ChasinSpin/SkyPilot/pifinder/3DPrinted/PiFinderLensCover/PiFinderLensCover.3mf

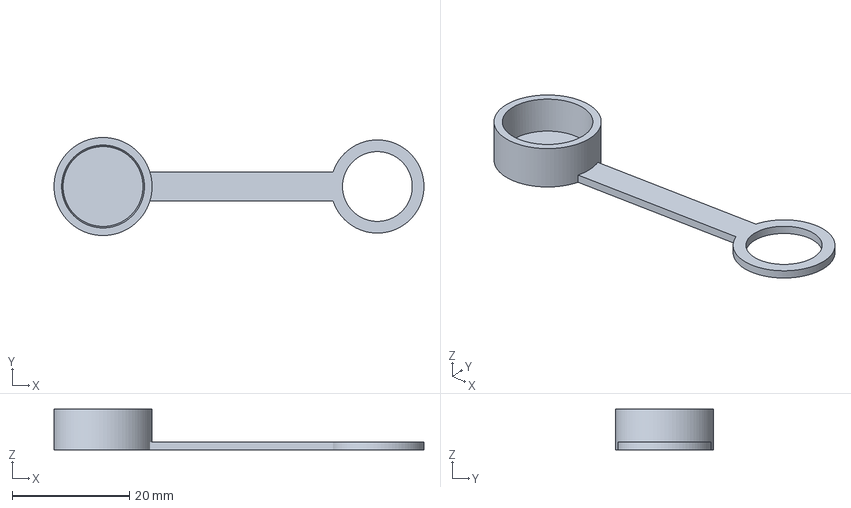
[picture p20: CAD file, 2024-11-16]
pifinder/3DPrinted/PiFinderLensCover/PiFinderLensCover.3mf
63.0 x 16.7 x 6.90 mm
