ChasinSpin/SkyPilot/dome/GPS/GPSCableClip.3mf

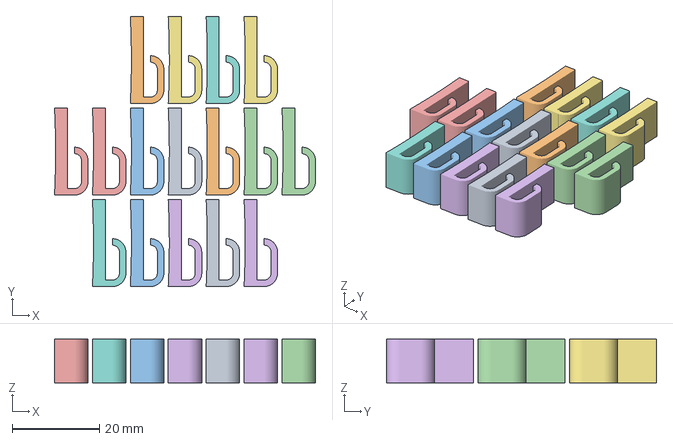
[picture p21: CAD file, 2024-11-11]
dome/GPS/GPSCableClip.3mf
59.9 x 62.0 x 10.0 mm
GPSCableClip.stl x 16
