ChasinSpin/SkyPilot/dome/TriBahtinovMask_ClubC14/TriBahtinovCover.3mf

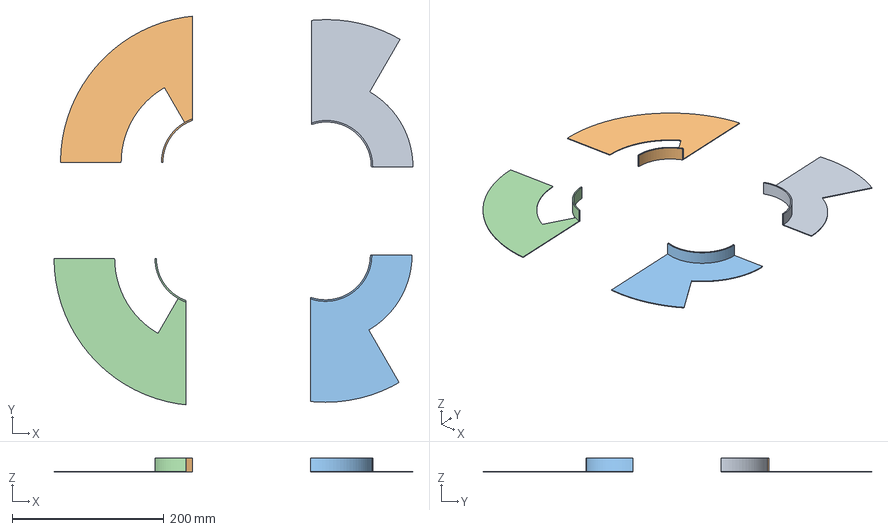
[picture p22: CAD file, 2025-02-14]
dome/TriBahtinovMask_ClubC14/TriBahtinovCover.3mf
473.1 x 512.0 x 19.0 mm
TriBahtinovCover.stl_A_A
TriBahtinovCover.stl_A_B
TriBahtinovCover.stl_B_A
TriBahtinovCover.stl_B_B
