ChasinSpin/SkyPilot/goto/3DPrinted/decRJ45Plate.3mf

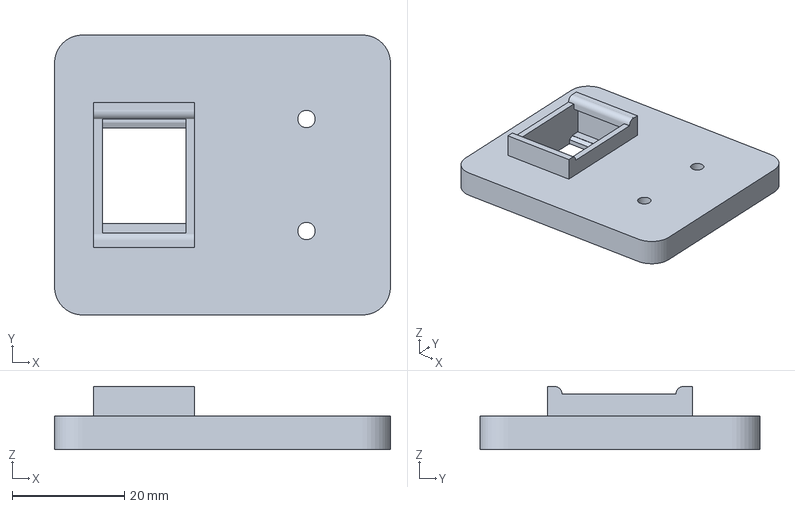
[picture p23: CAD file, 2025-01-19]
goto/3DPrinted/decRJ45Plate.3mf
60.0 x 50.0 x 11.2 mm
