ChasinSpin/SkyPilot/pifinder/3DPrinted/C14PiFinderHolder/clamp.stl

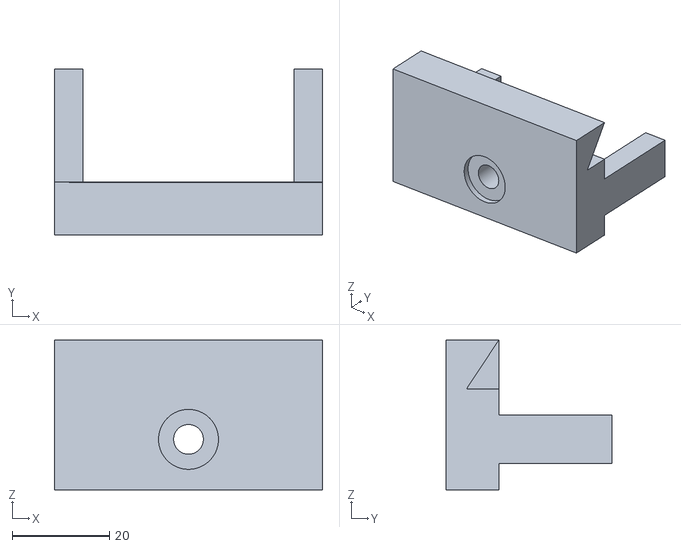
[picture p24: CAD file, 2024-11-16]
pifinder/3DPrinted/C14PiFinderHolder/clamp.stl
55.0 x 34.0 x 30.7
