ChasinSpin/SkyPilot/pifinder/3DPrinted/PiFinder/shroud.stl

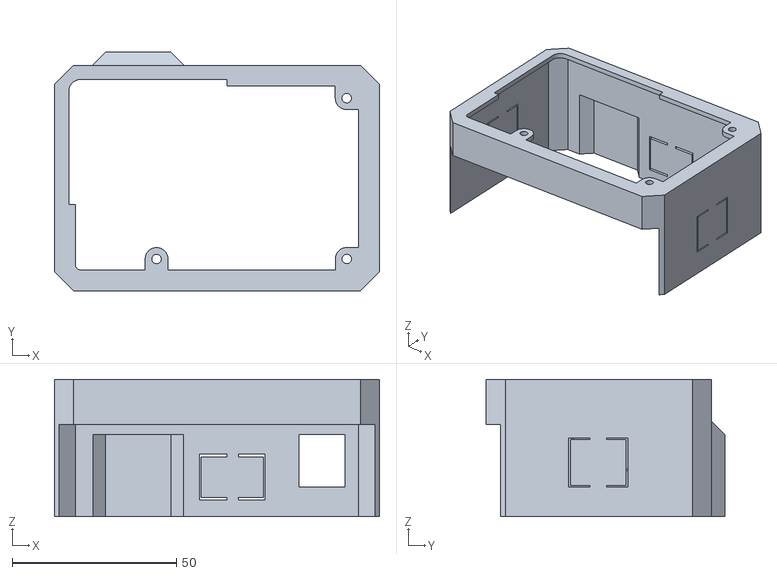
[picture p25: CAD file, 2024-11-16]
pifinder/3DPrinted/PiFinder/shroud.stl
99.1 x 72.7 x 41.8
