ChasinSpin/SkyPilot/dome/GPS/GPSBracketCovers.3mf

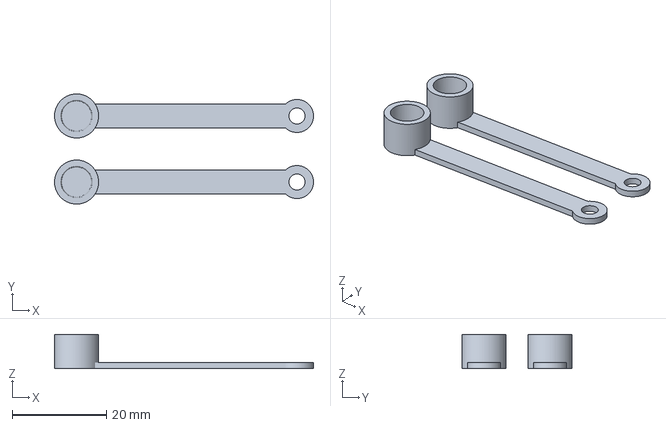
[picture p26: CAD file, 2024-11-11]
dome/GPS/GPSBracketCovers.3mf
54.9 x 23.3 x 7.30 mm
