ChasinSpin/SkyPilot/dome/TriBahtinovMask_ClubC14/TriBahtinovMask.3mf

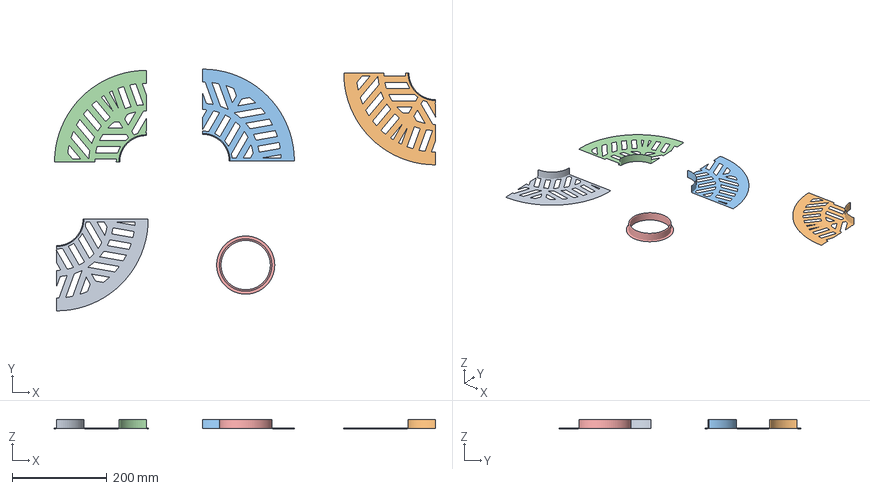
[picture p27: CAD file, 2025-02-14]
dome/TriBahtinovMask_ClubC14/TriBahtinovMask.3mf
805.6 x 511.2 x 20.0 mm
TriBahtinovMask.stl_A_A
TriBahtinovMask.stl_A_B
TriBahtinovMask.stl_B_A
TriBahtinovMask.stl_B_B
TriBahtinovCenterSupport.stl
