ChasinSpin/SkyPilot/goto/3DPrinted/controllerFacePlates.3mf

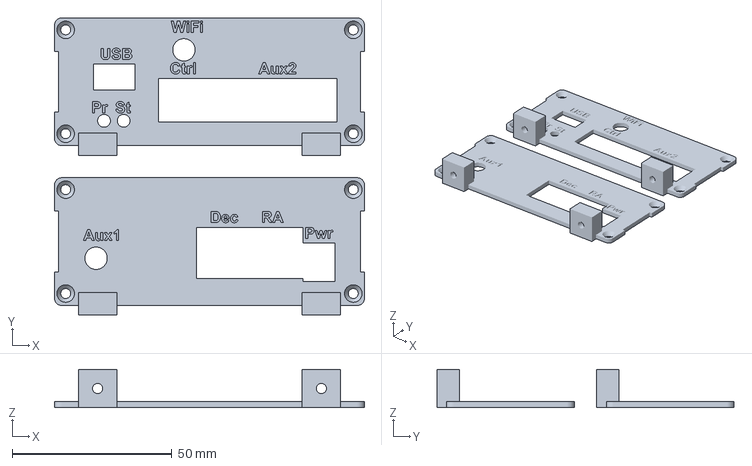
[picture p28: CAD file, 2025-01-19]
goto/3DPrinted/controllerFacePlates.3mf
97.0 x 93.0 x 12.0 mm
