ChasinSpin/SkyPilot/pifinder/3DPrinted/C14PiFinderHolder/knobCap.stl

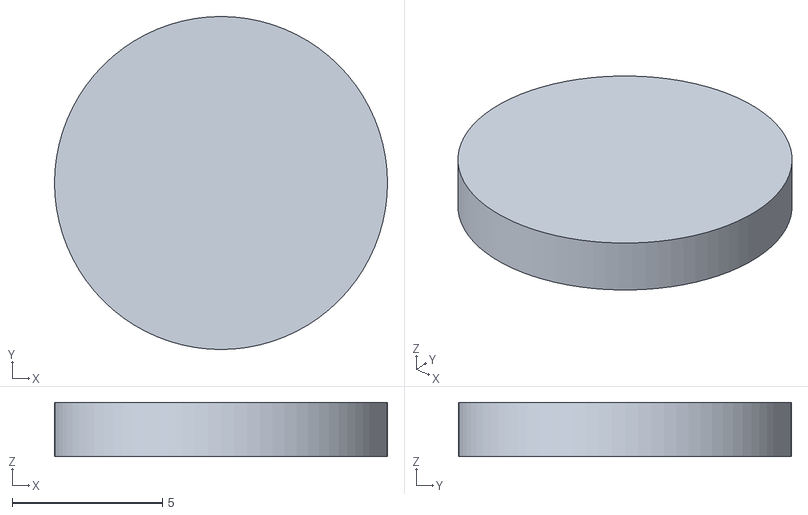
[picture p29: CAD file, 2024-11-16]
pifinder/3DPrinted/C14PiFinderHolder/knobCap.stl
11.1 x 11.1 x 1.80
