ChasinSpin/SkyPilot/pifinder/3DPrinted/PiFinder/focus_spacer.stl

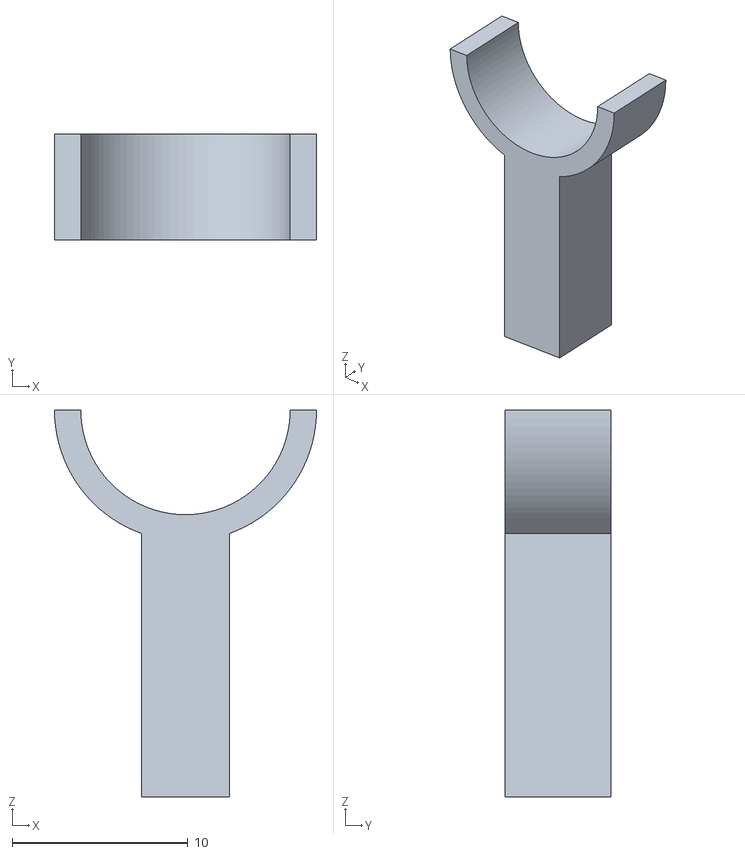
[picture p30: CAD file, 2024-11-16]
pifinder/3DPrinted/PiFinder/focus_spacer.stl
14.9 x 6.00 x 22.0
