ChasinSpin/SkyPilot/goto/3DPrinted/decOuterCasingBottom.3mf

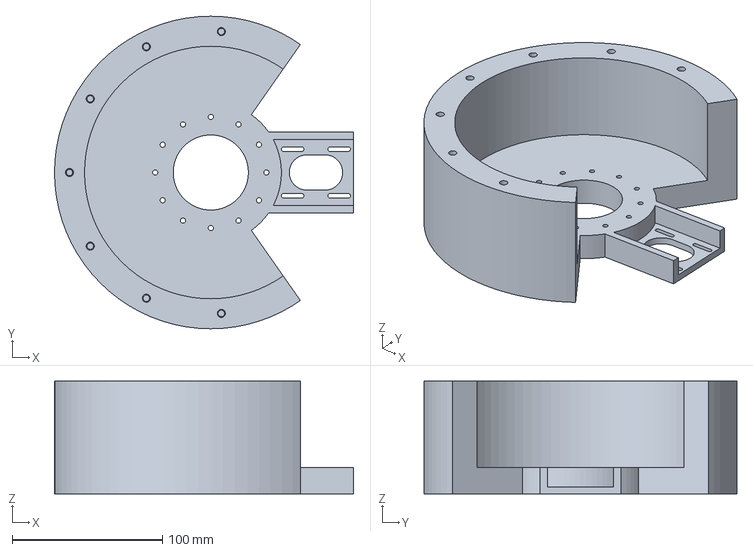
[picture p31: CAD file, 2025-01-19]
goto/3DPrinted/decOuterCasingBottom.3mf
199.1 x 208.1 x 75.0 mm
