ChasinSpin/SkyPilot/pifinder/3DPrinted/C14PiFinderHolder/mount.stl

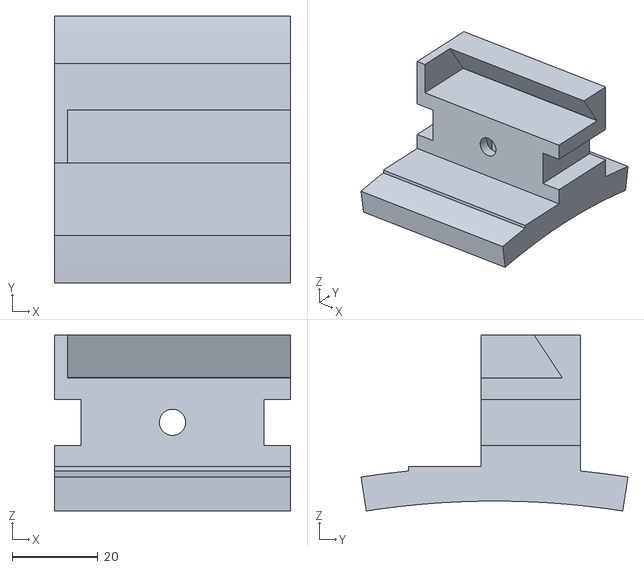
[picture p32: CAD file, 2024-11-16]
pifinder/3DPrinted/C14PiFinderHolder/mount.stl
55.0 x 62.2 x 41.0
