ChasinSpin/SkyPilot/pifinder/3DPrinted/PiFinder/dovetail_bottom.stl

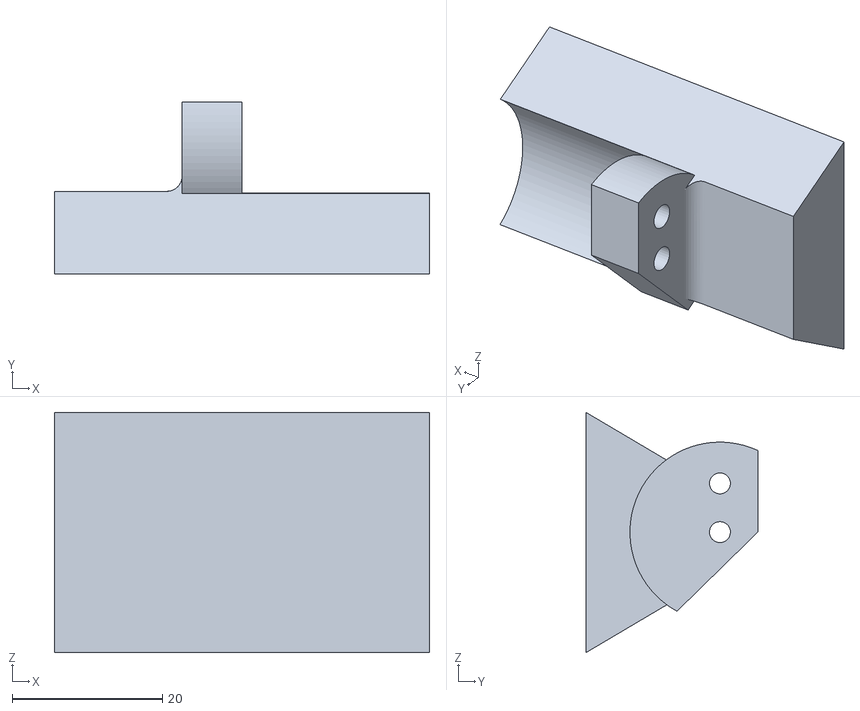
[picture p33: CAD file, 2024-11-16]
pifinder/3DPrinted/PiFinder/dovetail_bottom.stl
50.0 x 22.9 x 32.0
