ChasinSpin/SkyPilot/goto/3DPrinted/decRotationIndicator.3mf

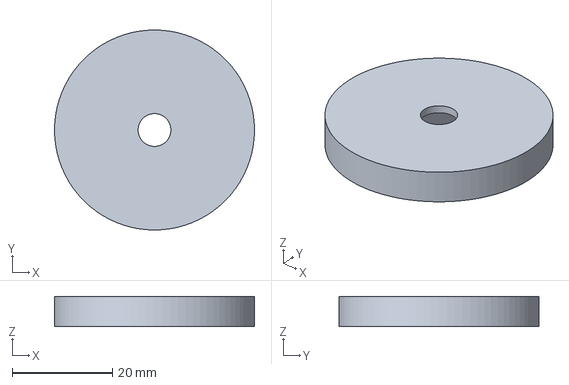
[picture p34: CAD file, 2025-01-19]
goto/3DPrinted/decRotationIndicator.3mf
40.0 x 40.0 x 6.00 mm
