ChasinSpin/SkyPilot/pifinder/3DPrinted/C14PiFinderHolder/C14PiFinderHolder.3mf

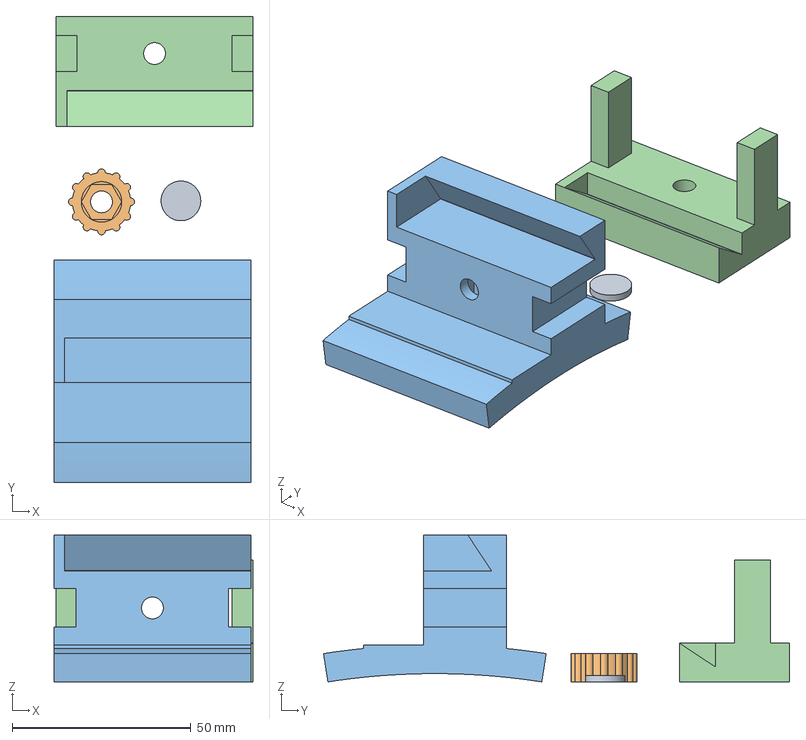
[picture p35: CAD file, 2024-11-16]
pifinder/3DPrinted/C14PiFinderHolder/C14PiFinderHolder.3mf
55.6 x 130.2 x 41.0 mm
knobCap.stl
knob.stl
mount.stl
clamp.stl
