ChasinSpin/SkyPilot/pifinder/3DPrinted/PiFinder/v25_camera_holddown.stl

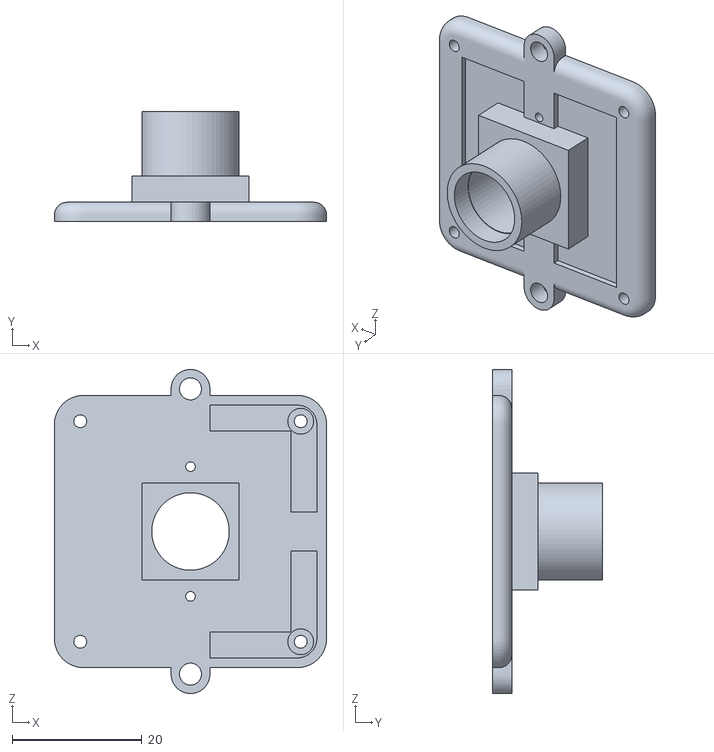
[picture p36: CAD file, 2024-11-16]
pifinder/3DPrinted/PiFinder/v25_camera_holddown.stl
42.0 x 17.0 x 50.0
