ChasinSpin/SkyPilot/goto/3DPrinted/declinationCoupler.3mf

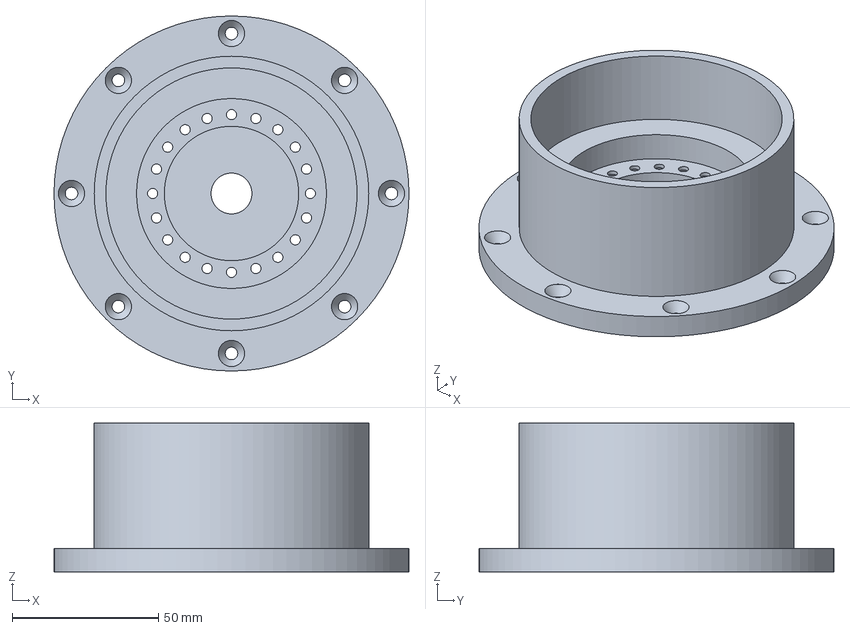
[picture p37: CAD file, 2025-01-19]
goto/3DPrinted/declinationCoupler.3mf
121.6 x 121.6 x 51.0 mm
