ChasinSpin/SkyPilot/pifinder/3DPrinted/PiFinder/v25_adapter.stl

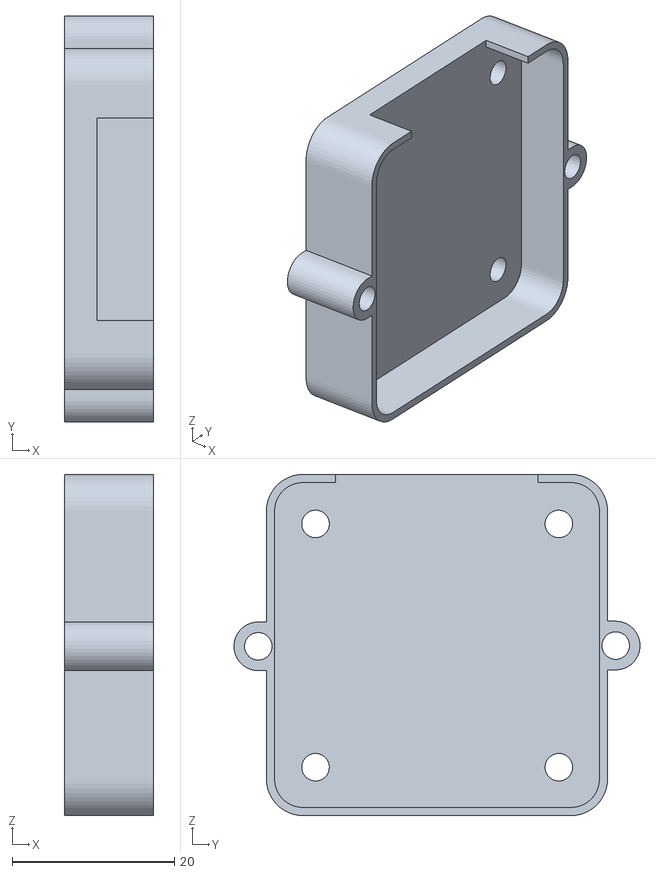
[picture p38: CAD file, 2024-11-16]
pifinder/3DPrinted/PiFinder/v25_adapter.stl
11.0 x 50.0 x 42.0
