ChasinSpin/SkyPilot/goto/3DPrinted/byersCasePlate.3mf

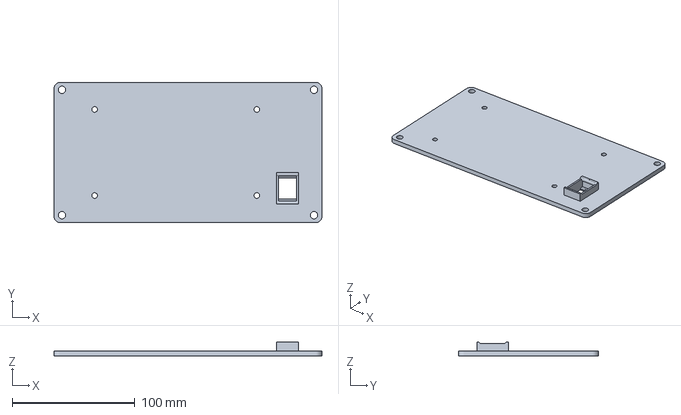
[picture p39: CAD file, 2025-01-19]
goto/3DPrinted/byersCasePlate.3mf
218.0 x 114.0 x 11.2 mm
