ChasinSpin/SkyPilot/pifinder/3DPrinted/PiFinder/back.stl

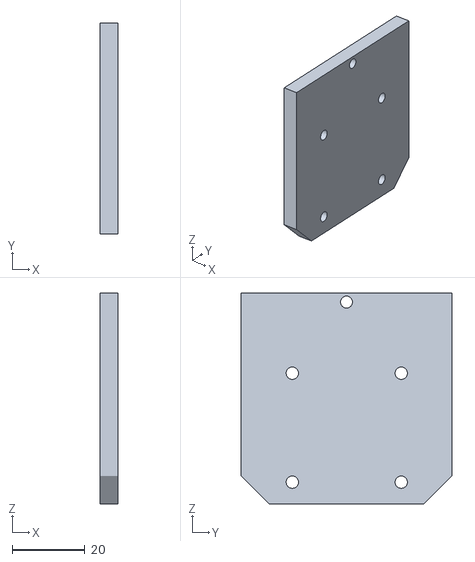
[picture p40: CAD file, 2024-11-16]
pifinder/3DPrinted/PiFinder/back.stl
5.00 x 58.0 x 58.0
