ChasinSpin/SkyPilot/goto/3DPrinted/decOuterCasingTop.3mf

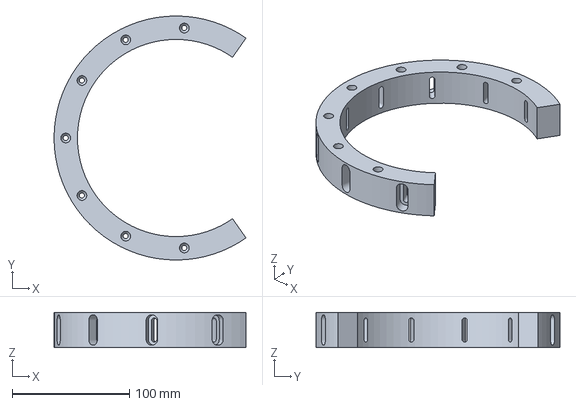
[picture p41: CAD file, 2025-01-19]
goto/3DPrinted/decOuterCasingTop.3mf
163.7 x 208.1 x 30.0 mm
