ChasinSpin/SkyPilot/pifinder/3DPrinted/PiFinder/pi_mount.stl

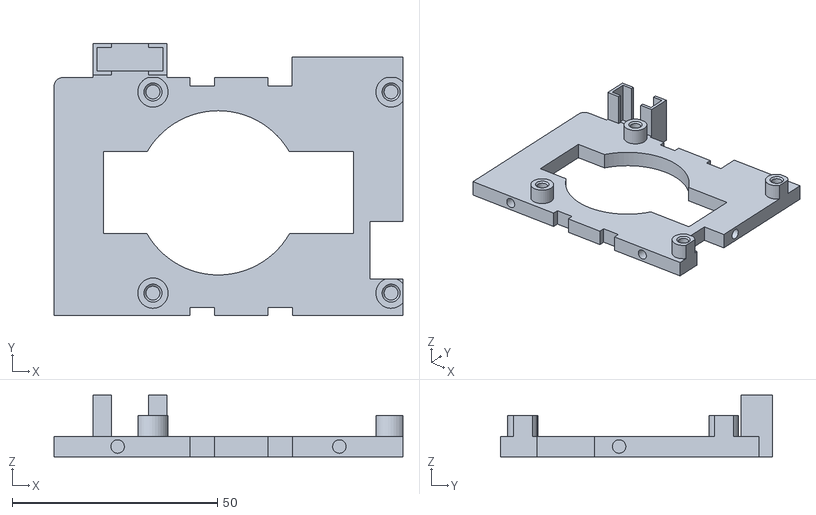
[picture p42: CAD file, 2024-11-16]
pifinder/3DPrinted/PiFinder/pi_mount.stl
85.0 x 66.3 x 15.0
