ChasinSpin/SkyPilot/goto/3DPrinted/decCover.3mf

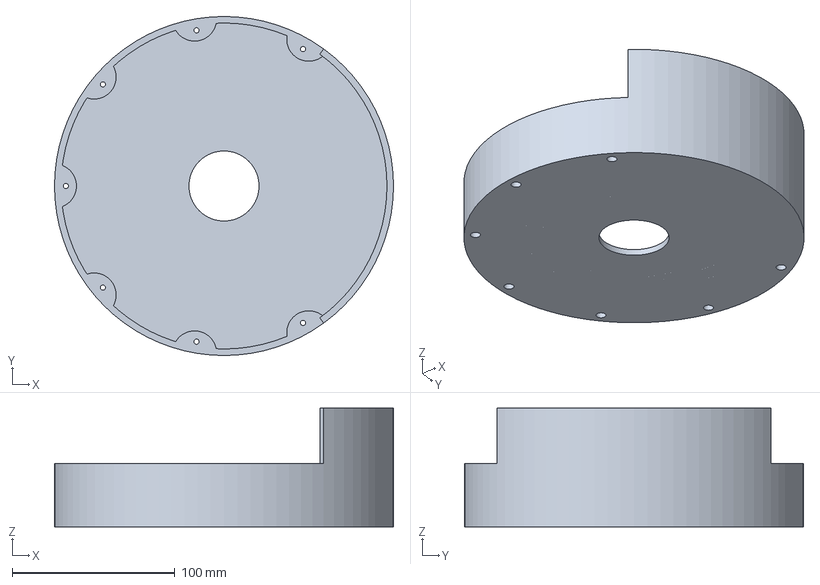
[picture p43: CAD file, 2025-01-19]
goto/3DPrinted/decCover.3mf
208.1 x 208.1 x 73.0 mm
