ChasinSpin/SkyPilot/pifinder/3DPrinted/PiFinder/bezel.stl

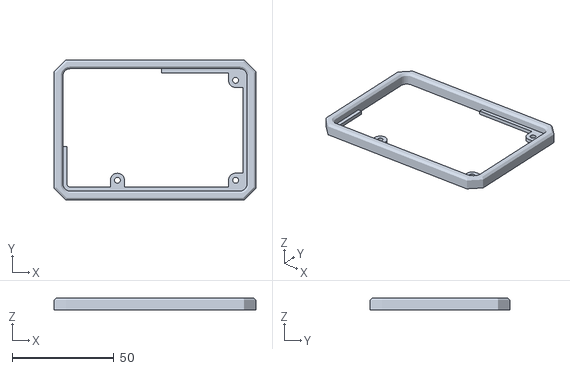
[picture p44: CAD file, 2024-11-16]
pifinder/3DPrinted/PiFinder/bezel.stl
99.1 x 68.7 x 5.80
