ChasinSpin/SkyPilot/goto/3DPrinted/byersCaseExtension.3mf

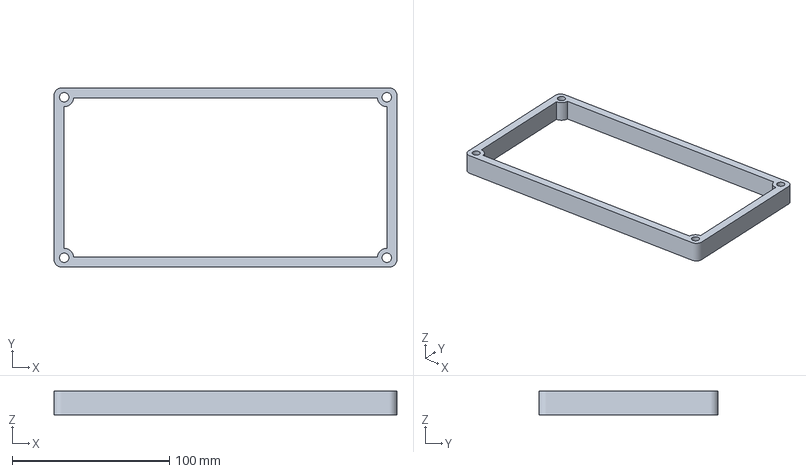
[picture p45: CAD file, 2025-01-19]
goto/3DPrinted/byersCaseExtension.3mf
218.0 x 114.0 x 15.0 mm
