ChasinSpin/SkyPilot/pifinder/3DPrinted/PiFinder/bottom.stl

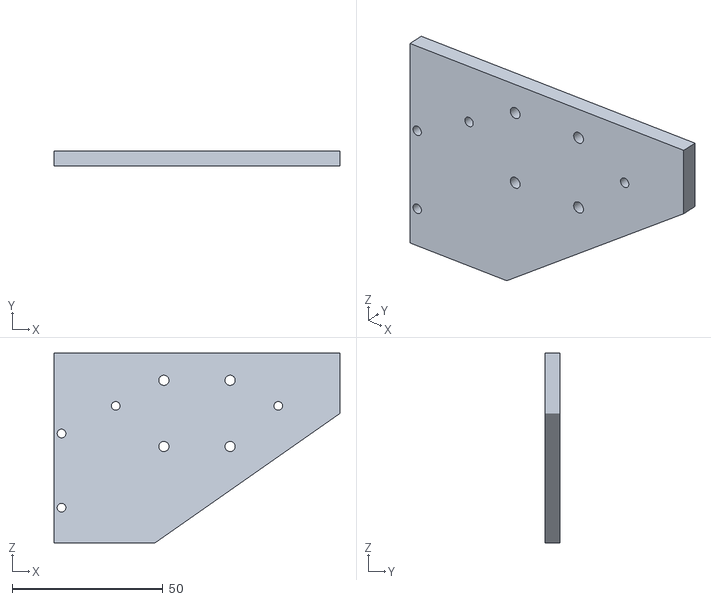
[picture p46: CAD file, 2024-11-16]
pifinder/3DPrinted/PiFinder/bottom.stl
95.0 x 5.00 x 63.0
