ChasinSpin/SkyPilot/goto/3DPrinted/clamps.stl

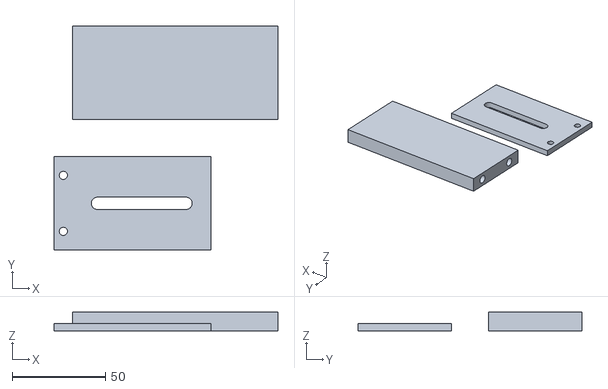
[picture p47: CAD file, 2025-01-12]
goto/3DPrinted/clamps.stl
120.0 x 120.0 x 10.0
