ChasinSpin/SkyPilot/pifinder/3DPrinted/PiFinder/PiFinder.3mf

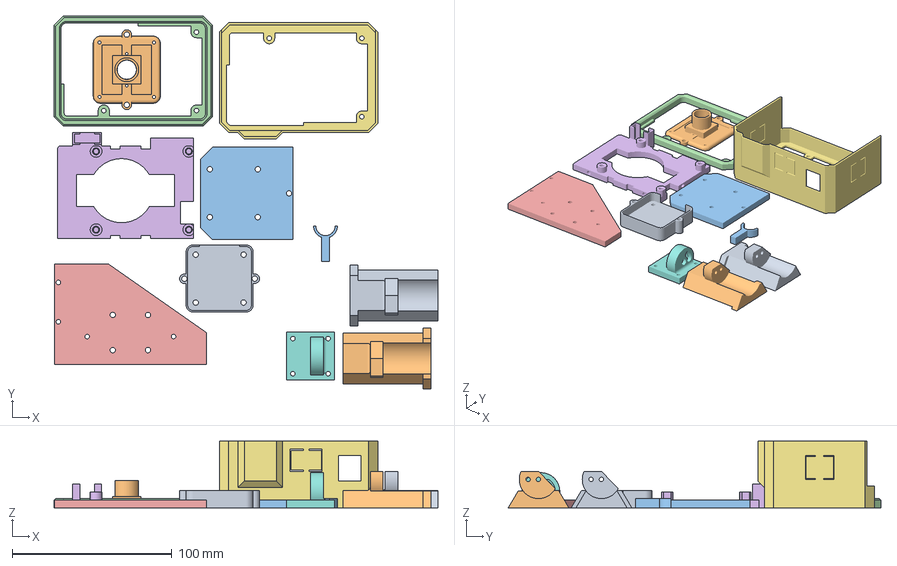
[picture p48: CAD file, 2024-11-16]
pifinder/3DPrinted/PiFinder/PiFinder.3mf
240.1 x 233.0 x 41.8 mm
v25_adapter.stl
v25_camera_holddown.stl
back.stl
bezel.stl
bottom.stl
pi_mount.stl
shroud.stl
dovetail_top.stl
dovetail_bottom_hardstop_left.stl
dovetail_bottom_hardstop_right.stl
focus_spacer.stl
