ChasinSpin/SkyPilot/goto/3DPrinted/decBearingPlate.3mf

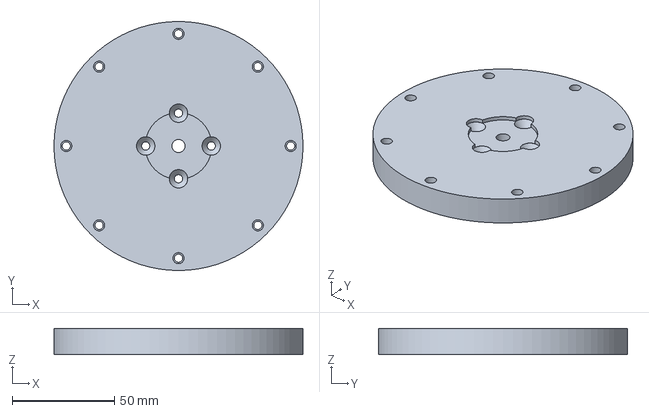
[picture p49: CAD file, 2025-01-12]
goto/3DPrinted/decBearingPlate.3mf
121.5 x 121.6 x 12.9 mm
