ChasinSpin/SkyPilot/pifinder/3DPrinted/PiFinder/dovetail_top.stl

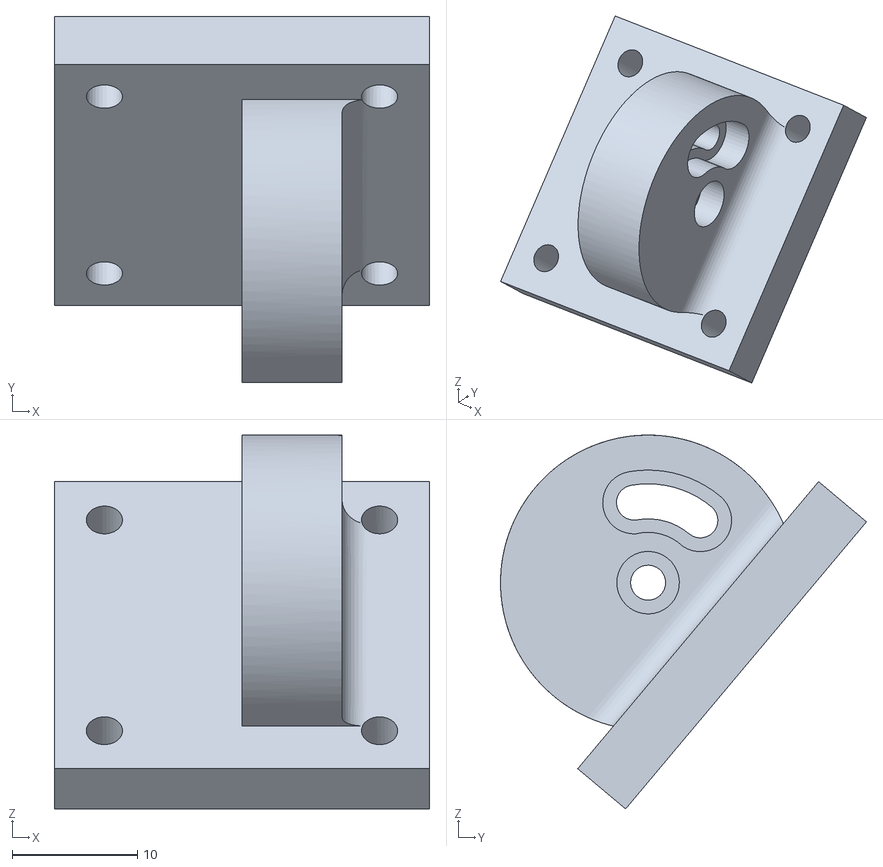
[picture p50: CAD file, 2024-11-16]
pifinder/3DPrinted/PiFinder/dovetail_top.stl
30.0 x 29.3 x 29.9
