ChasinSpin/SkyPilot/goto/3DPrinted/raStepperPlate.3mf

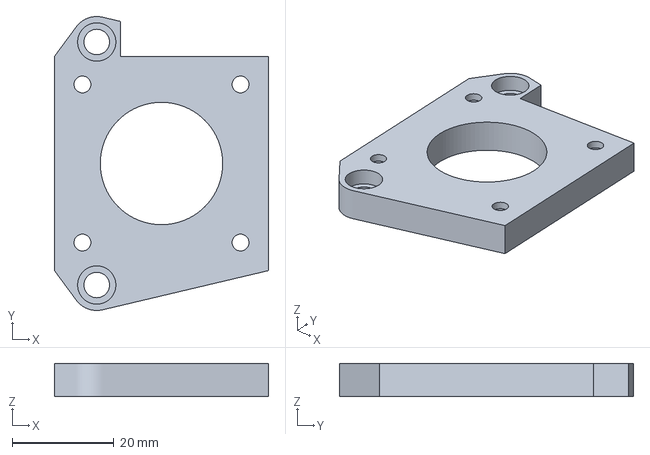
[picture p51: CAD file, 2025-01-12]
goto/3DPrinted/raStepperPlate.3mf
42.0 x 57.7 x 6.50 mm
